ambraglow/VLF-receiver/board-images/DSC_1119.jpg

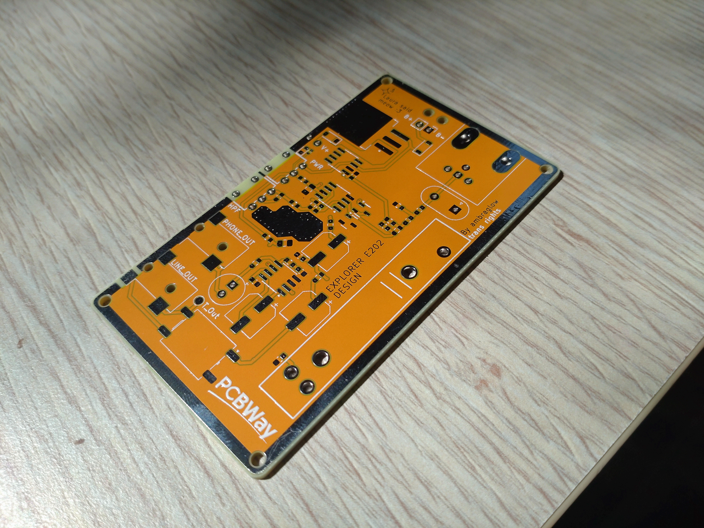
board-images/DSC_1119.jpg
