ambraglow/VLF-receiver/board-images/DSC_1122.jpg

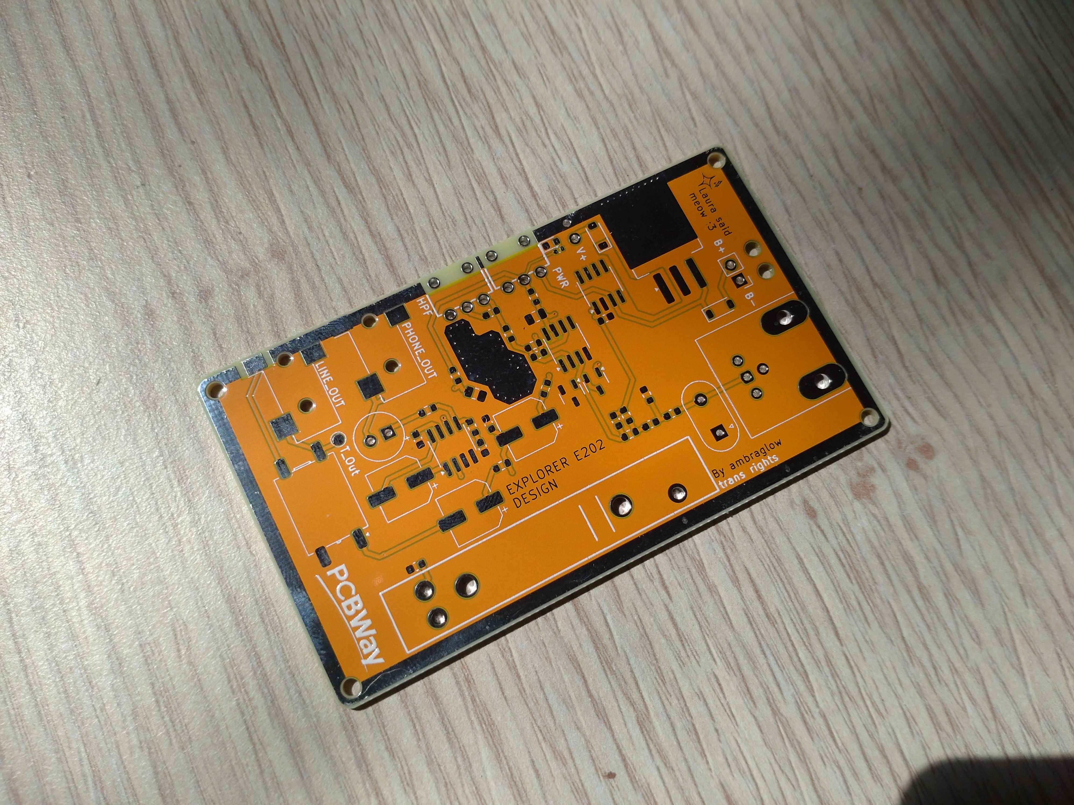
board-images/DSC_1122.jpg
