ambraglow/VLF-receiver/board-images/DSC_1123.jpg

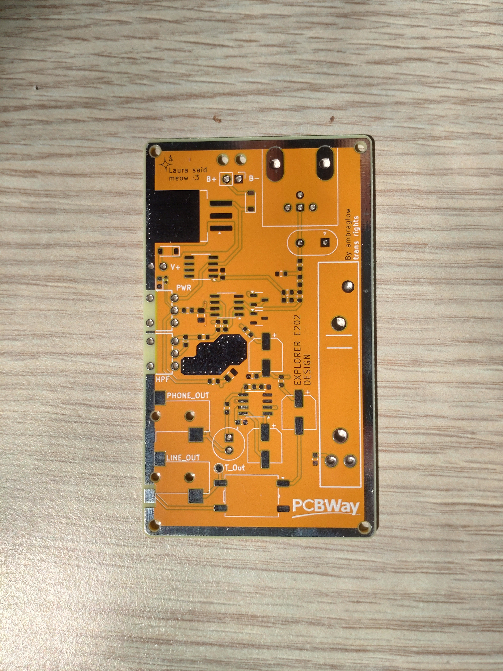
board-images/DSC_1123.jpg
