ambraglow/VLF-receiver/board-images/DSC_1124.jpg

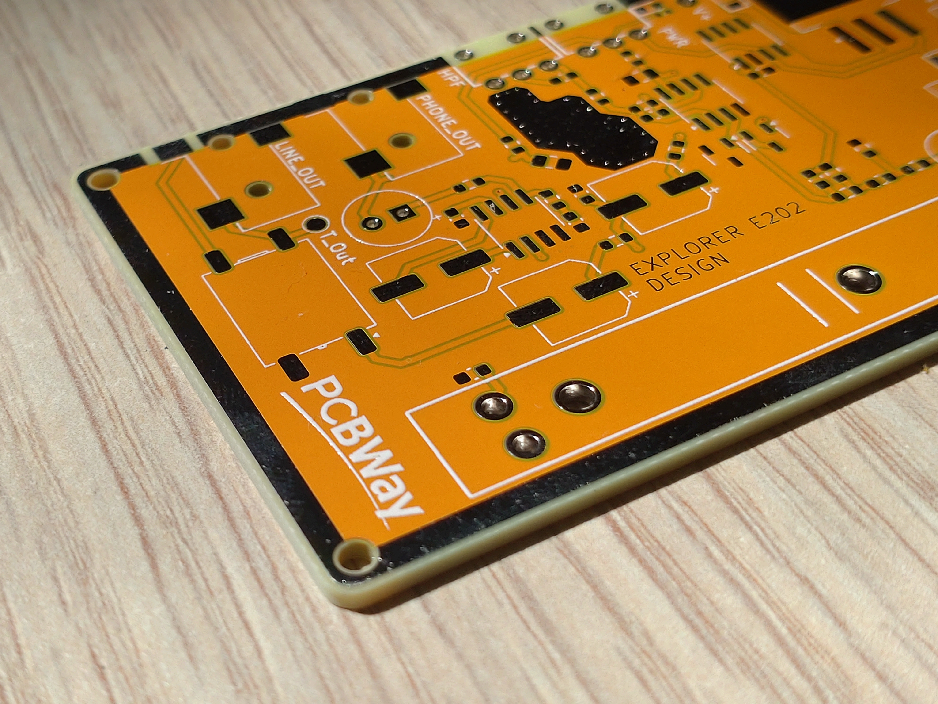
board-images/DSC_1124.jpg
