ambraglow/VLF-receiver/board-images/DSC_1125.jpg

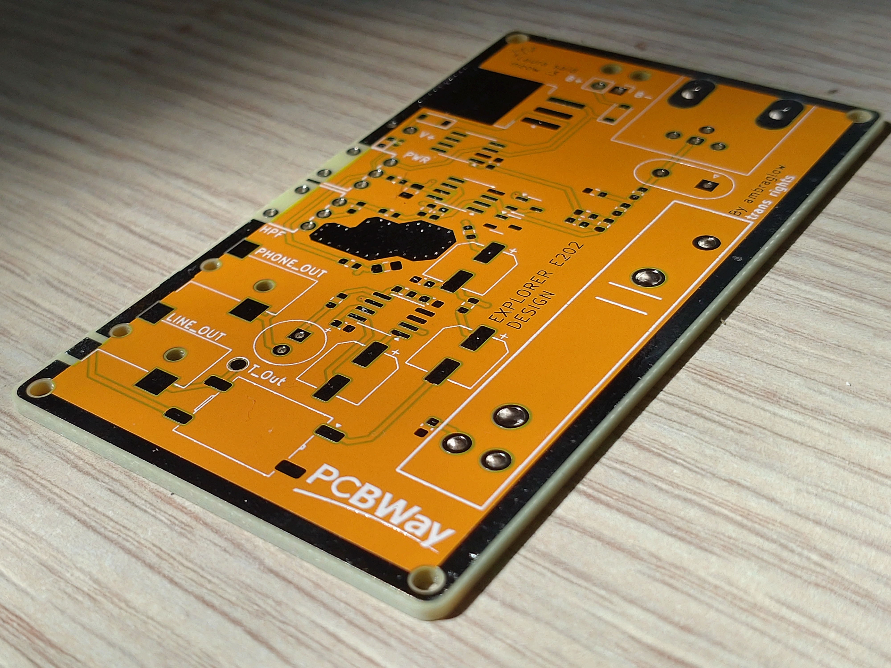
board-images/DSC_1125.jpg
